talhatallat/Weight-Measurement-System/Block diagram/BD.png

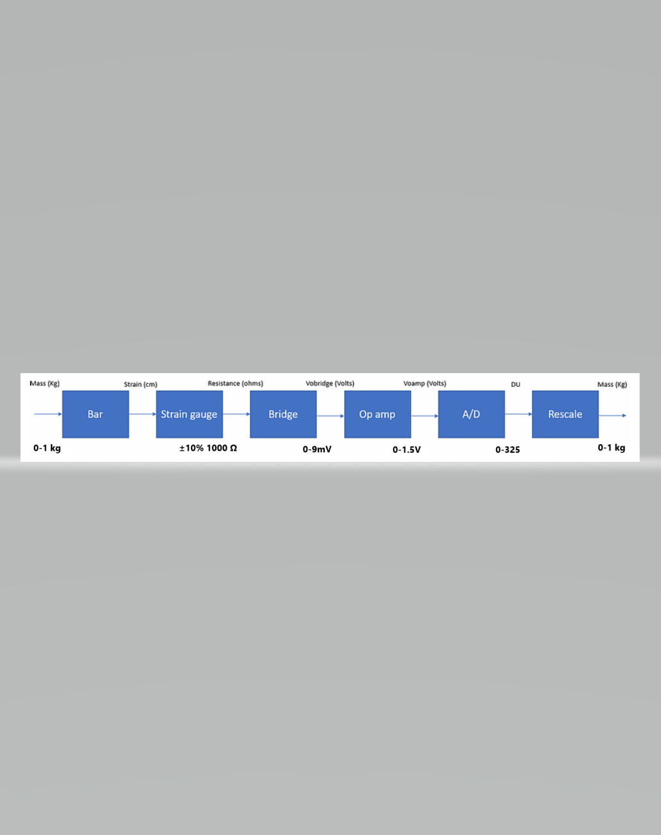
Block diagram/BD.png
