talhatallat/Weight-Measurement-System/Weight messurment device images/131050956_479906776314056_5110399193145118110_n.png

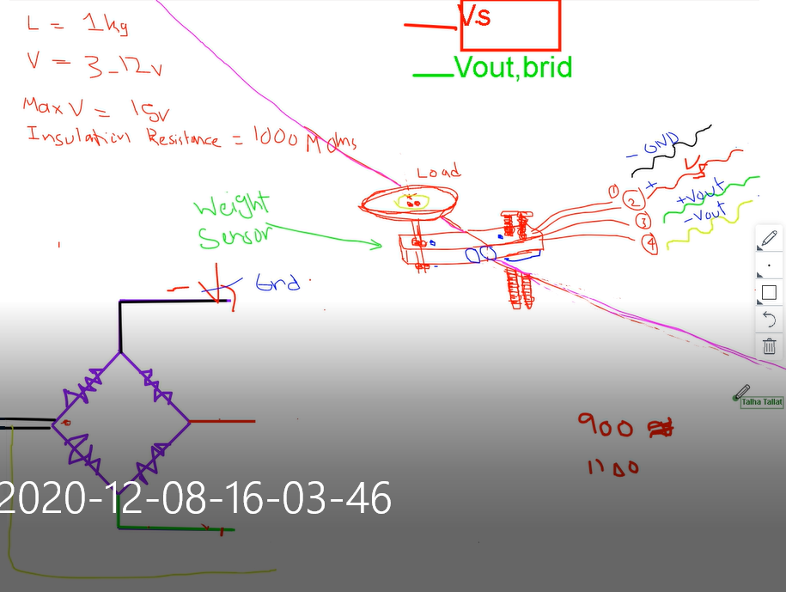
Weight messurment device images/131050956_479906776314056_5110399193145118110_n.png
