talhatallat/Weight-Measurement-System/Weight messurment device images/Capture.JPG

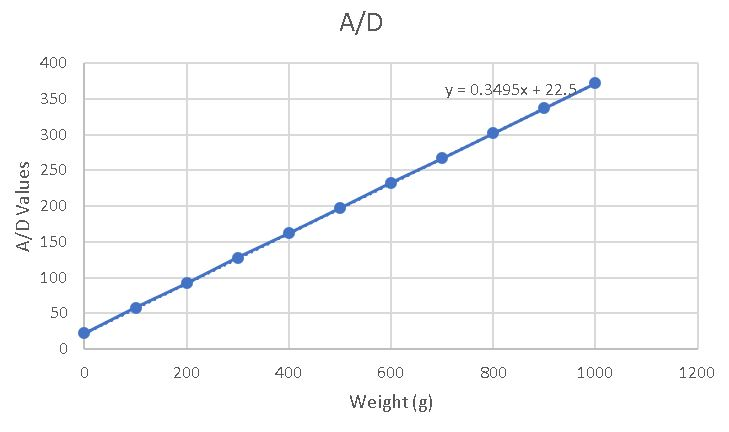
Weight messurment device images/Capture.JPG
