talhatallat/Weight-Measurement-System/Weight messurment device images/cell-and-wheatstone-1024x412.png

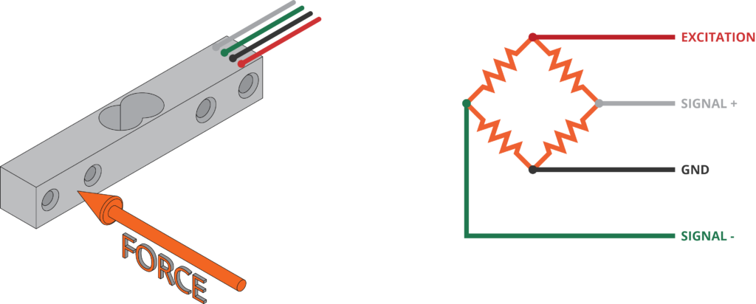
Weight messurment device images/cell-and-wheatstone-1024x412.png
