talhatallat/Weight-Measurement-System/Weight messurment device images/Load-Cell-Cantilever.jpg

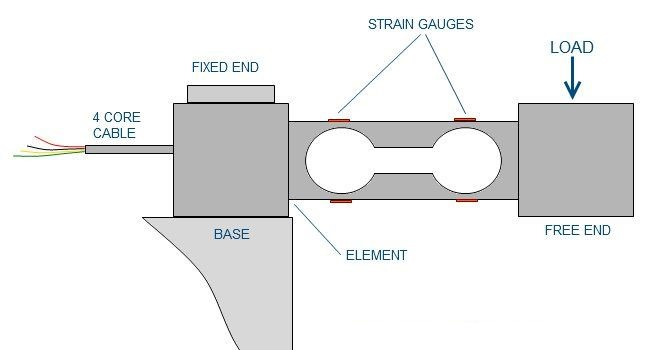
Weight messurment device images/Load-Cell-Cantilever.jpg
