talhatallat/Weight-Measurement-System/Weight messurment device images/LOAD-CELL.png

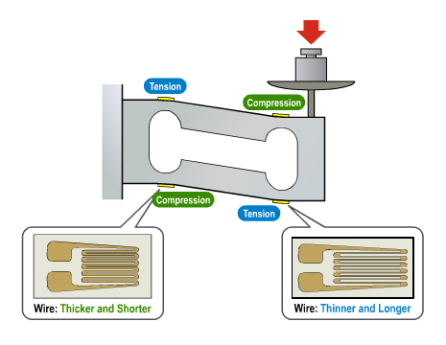
Weight messurment device images/LOAD-CELL.png
