talhatallat/Weight-Measurement-System/Weight messurment device images/tempsnip.png

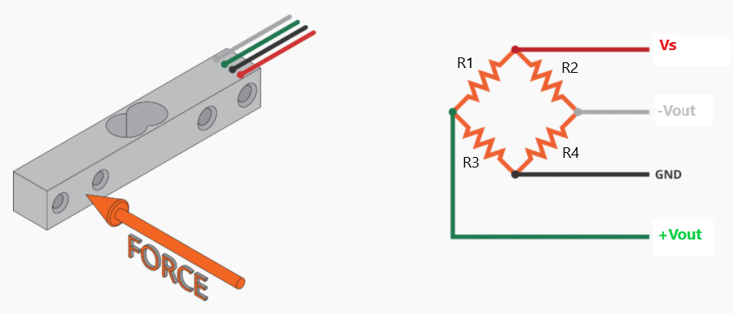
Weight messurment device images/tempsnip.png
