talhatallat/Weight-Measurement-System/Block diagram/BD_Fix.png

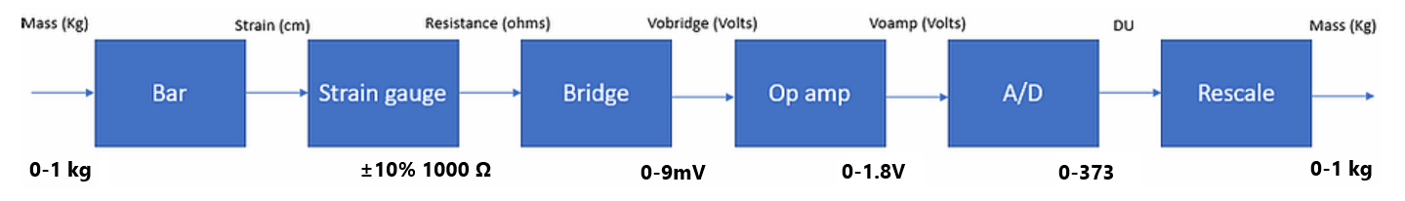
Block diagram/BD_Fix.png
